ajackson2681/codex/include/SystemState.hpp

#pragma once

#include "Config.hpp"

enum State 
{
    STARTUP,
    STARTUP_CARD_DETECTED,
    STARTUP_NO_CARD_DETECTED,
    DOCUMENT_SELECTION,
    SET_DOC_NAME,
    INITIALIZATION,
    WRITING
};

namespace SystemState 
{
    /**
     * @brief Returns the current state of the application
     * 
     * @return State 
     */
    State get();

    /**
     * @brief Sets the new state for the application. 
     * 
     * @param newState the state to switch to
     */
    void set(State newState);
};
