ajackson2681/codex/include/GapBuffer.hpp

#pragma once

#include <vector>
#include <string>
#include <cstdint>

#include "Config.hpp"

#define DEFAULT_BUF_SIZE 32

#define SHOW_GAP false

#define FRAME_SIZE (COL_COUNT * ROW_COUNT)

class GapBuffer {
private:
    char frameBuf[ROW_COUNT][COL_COUNT];

    std::vector<char> buffer;
    int gapStart;
    int gapEnd;    
    int viewFrameStart;
    int cursorRow;
    int cursorCol;
    // this is true if the buffer has been modified since the last time it was printed
    bool stale = true;
    bool cursorHasMoved = true;
    
    /**
     * @brief Resizese the buffer vector. It will double in size with each
     * call to this until the buffer reaches a size of 64k, and then it will
     * only increase in size by 8k increments until it hits 112k. At this point
     * the buffer will no longer grow.
     */
    void resize();

    void moveLeft(bool moveCursor);
    void moveRight(bool moveCursor);

    void moveCursorLeft();
    void moveCursorRight();

    void refreshFrameBuffer();

    int findPrevLineStart(int from);
    int findNextLineStart(int from);

    
    int frameCellToBufferIndex(int targetRow, int targetCol);
    void clamp();
    
public:
    GapBuffer(int initialSize = DEFAULT_BUF_SIZE);
    ~GapBuffer();

    /**
     * @brief insert a character at the current cursor position. This will 
     * resize the buffer if necessary.
     * 
     * @param c Character to insert
     */
    void insert(char c);
    
    /**
     * @brief insert a string at the current cursor postion. This will resize
     * the buffer if necessary.
     * 
     * @param str String to insert
     */
    void insert(const std::string& str);

    void insertNewlineAbove();
    void insertNewlineBelow();
    
    /**
     * @brief Moves the cursor left by one character
     */
    void moveLeft();
    
    /**
     * @brief Moves the cursor right by one character
     */
    void moveRight();

    /**
     * @brief Moves the cursor left by one word. A "word" in this case is
     * defined as a space-separated value
     */
    void moveWordLeft();

    /**
     * @brief Moves the cursor right by one word. A "word" in this case is
     * defined as a space-separated value
     */
    void moveWordRight();

    /**
     * @brief Moves the cursor to the very beginning of the buffer
     */
    void moveToStart();

    /**
     * @brief Moves cursor to the beginning of the current line
     * 
     */
    void moveToLineStart();

    /**
     * @brief Moves the cursor to the very end of the buffer
     */
    void moveToEnd();

    /**
     * @brief Moves cursor to the end of the current line
     * 
     */
    void moveToLineEnd();

    /**
     * @brief Moves the cursor up by one line relative to the frame buffer.
     * 
     */
    void moveUpOneLine();

    /**
     * @brief Moves the cursor down by one line relative to the frame buffer.
     * 
     */
    void moveDownOneLine();

    void moveToFrameStart();
    void moveToFrameEnd();

    void backSpace();
    void backSpaceWord();

    void deleteChar();
    void deleteWord();
    
    char getCharAt(int idx);
    
    int getFrameRow();
    int getFrameCol();

    inline void getCursorPos(int& row, int& col) {
        row = cursorRow; 
        col = cursorCol;
    }

    const char (&getVisibleFrame())[ROW_COUNT][COL_COUNT];
    void invalidate();
    bool isStale();
    bool cursorMoved();
    int totalChars();

    void clearBuffer();
};
